yellobyte/LED-Strip-Light-Organ/Doc/BoardBottom.JPG

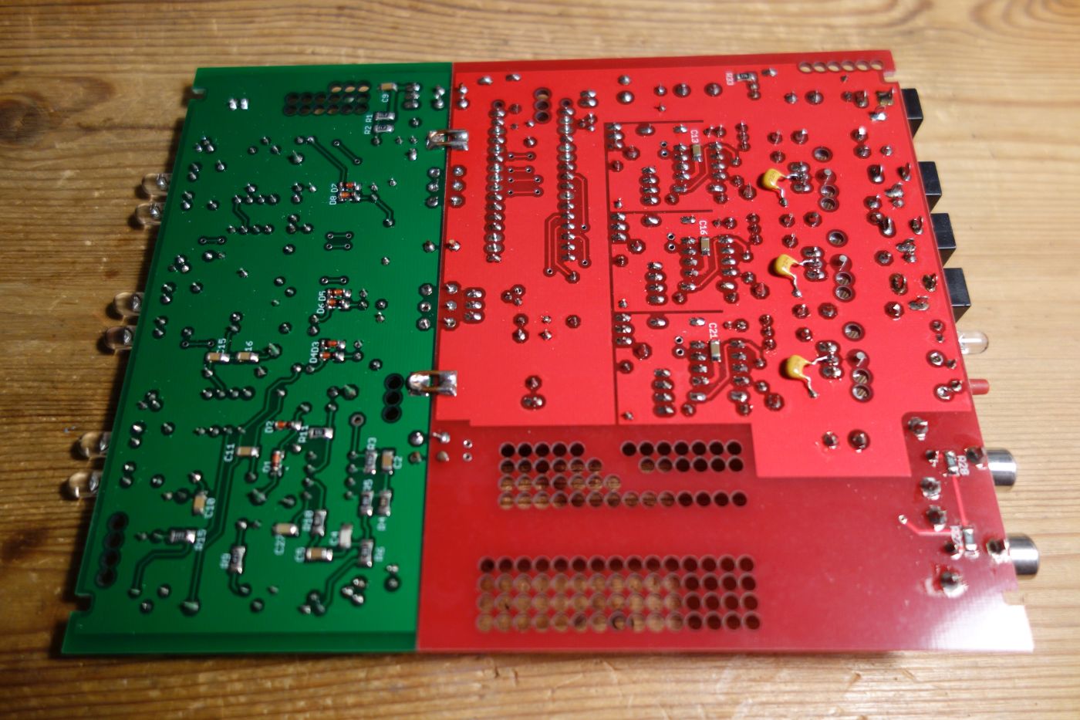
Doc/BoardBottom.JPG
