yellobyte/LED-Strip-Light-Organ/Doc/BoardTop.JPG

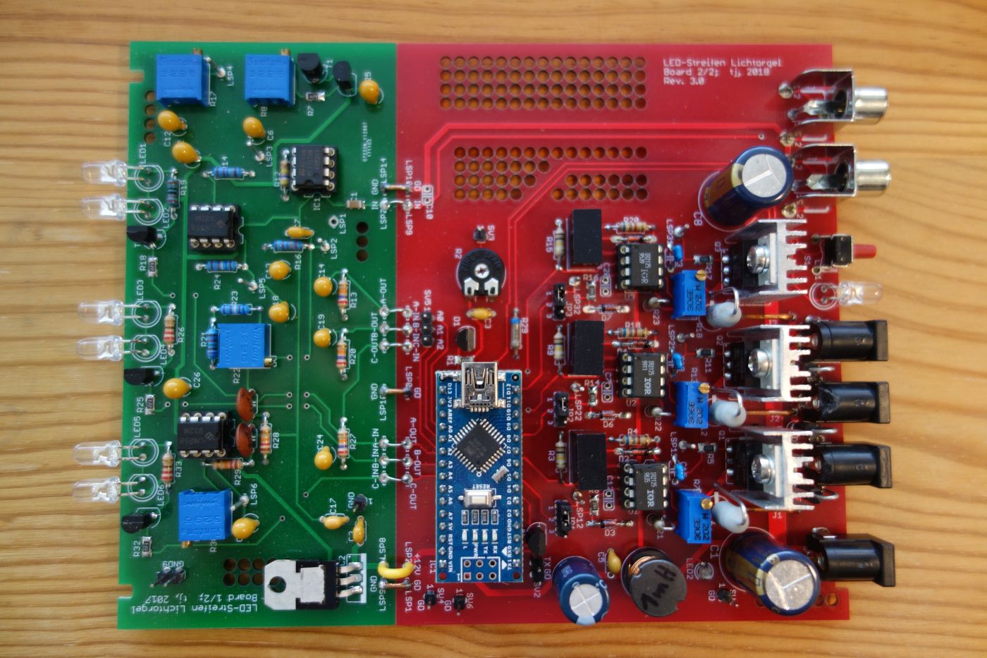
Doc/BoardTop.JPG
