yellobyte/LED-Strip-Light-Organ/Doc/FrontWithControlLEDs.JPG

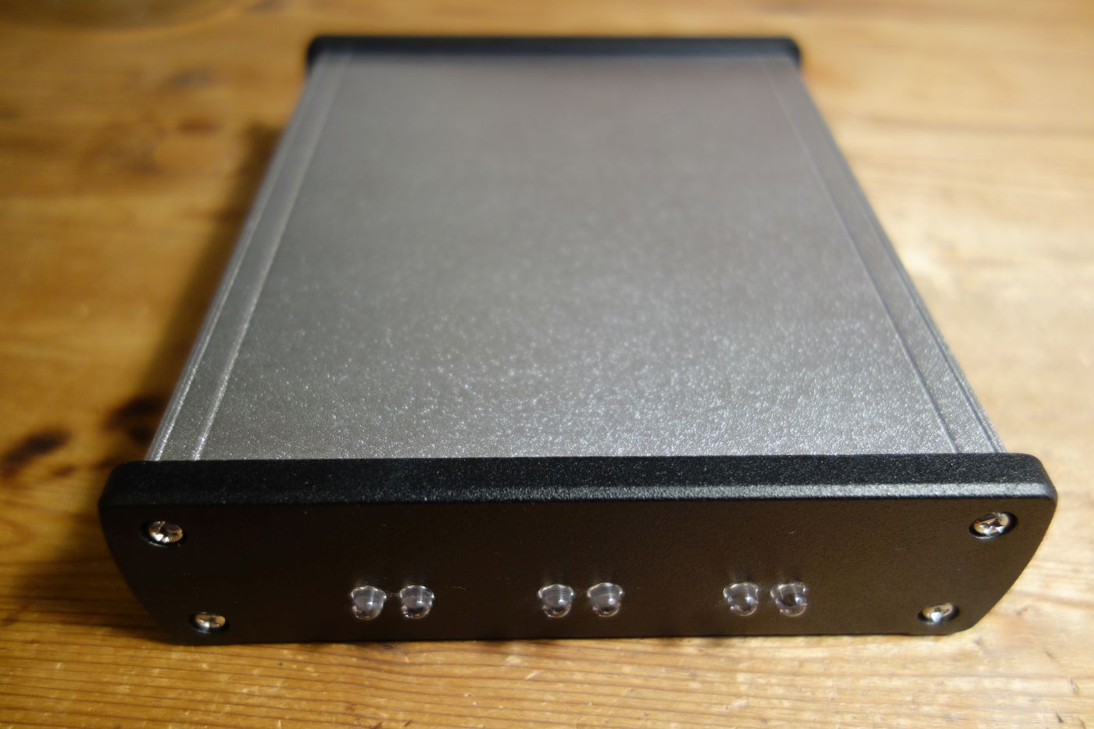
Doc/FrontWithControlLEDs.JPG
