yellobyte/LED-Strip-Light-Organ/EagleFiles/Filter-PCB/Board.JPG

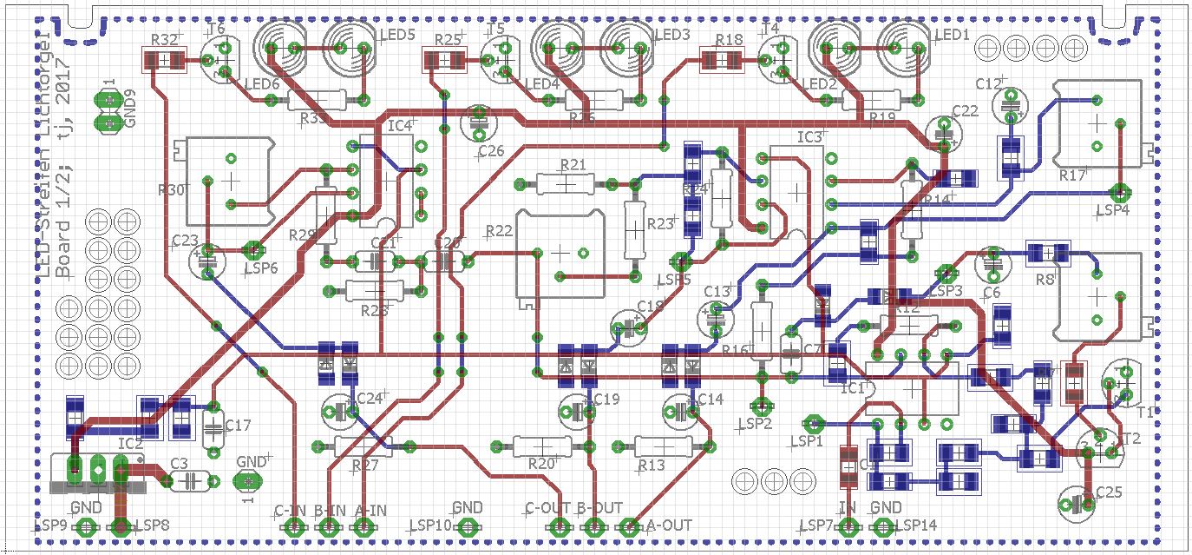
EagleFiles/Filter-PCB/Board.JPG
