yellobyte/LED-Strip-Light-Organ/EagleFiles/Filter-PCB/Filter Calculations/BandPass.JPG

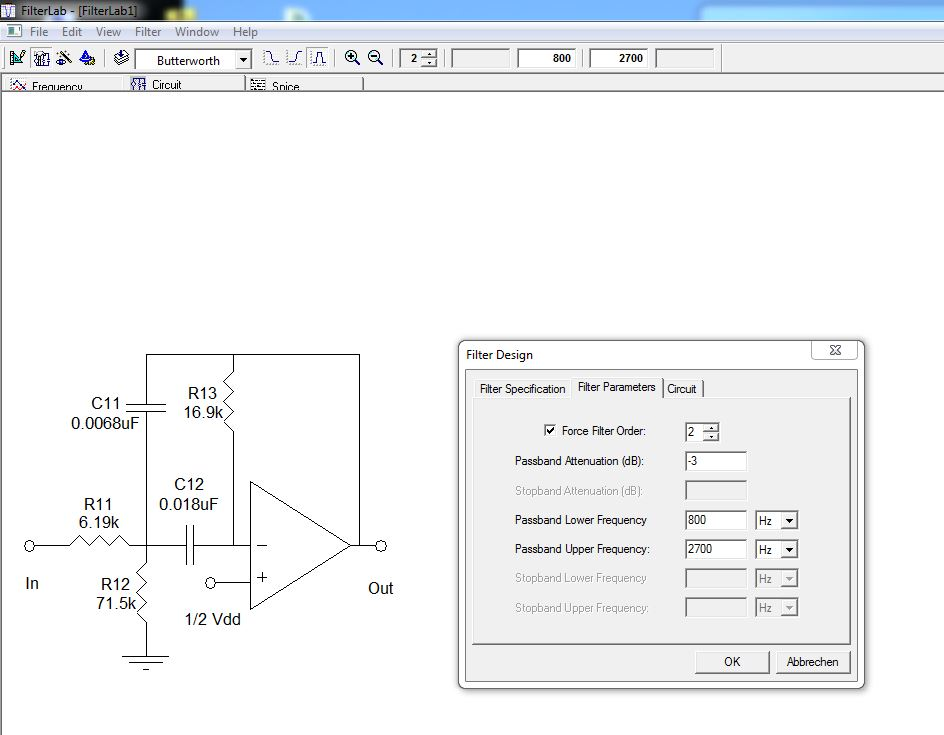
EagleFiles/Filter-PCB/Filter Calculations/BandPass.JPG
