yellobyte/LED-Strip-Light-Organ/EagleFiles/Filter-PCB/Filter Calculations/LowPass.JPG

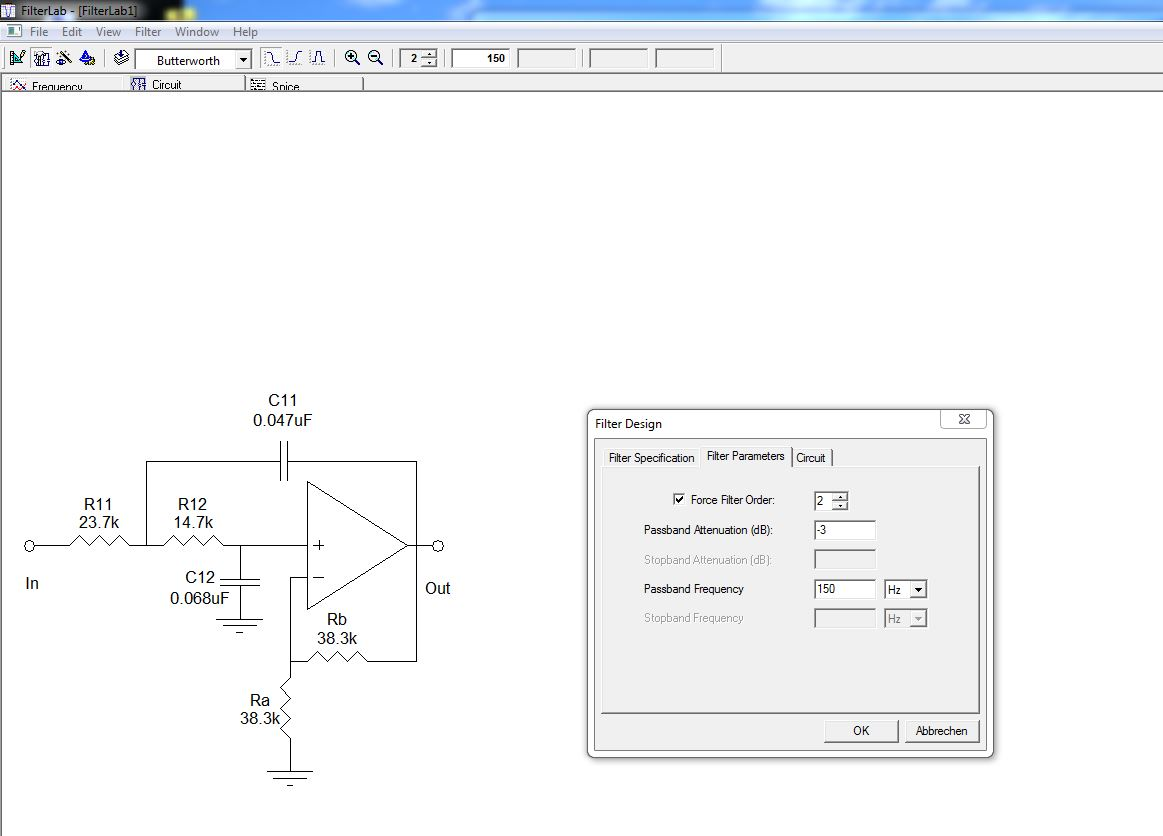
EagleFiles/Filter-PCB/Filter Calculations/LowPass.JPG
