yellobyte/LED-Strip-Light-Organ/EagleFiles/Filter-PCB/NetClasses.JPG

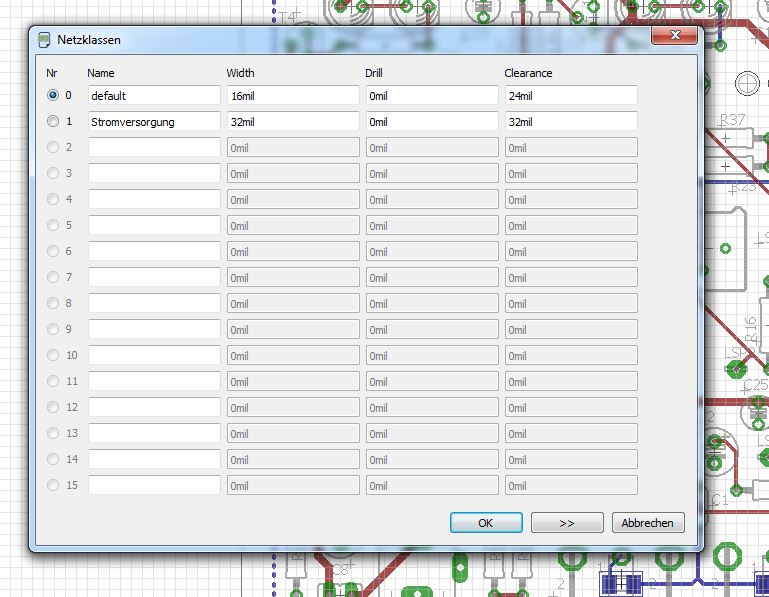
EagleFiles/Filter-PCB/NetClasses.JPG
