yellobyte/LED-Strip-Light-Organ/EagleFiles/Power-PCB/Board.JPG

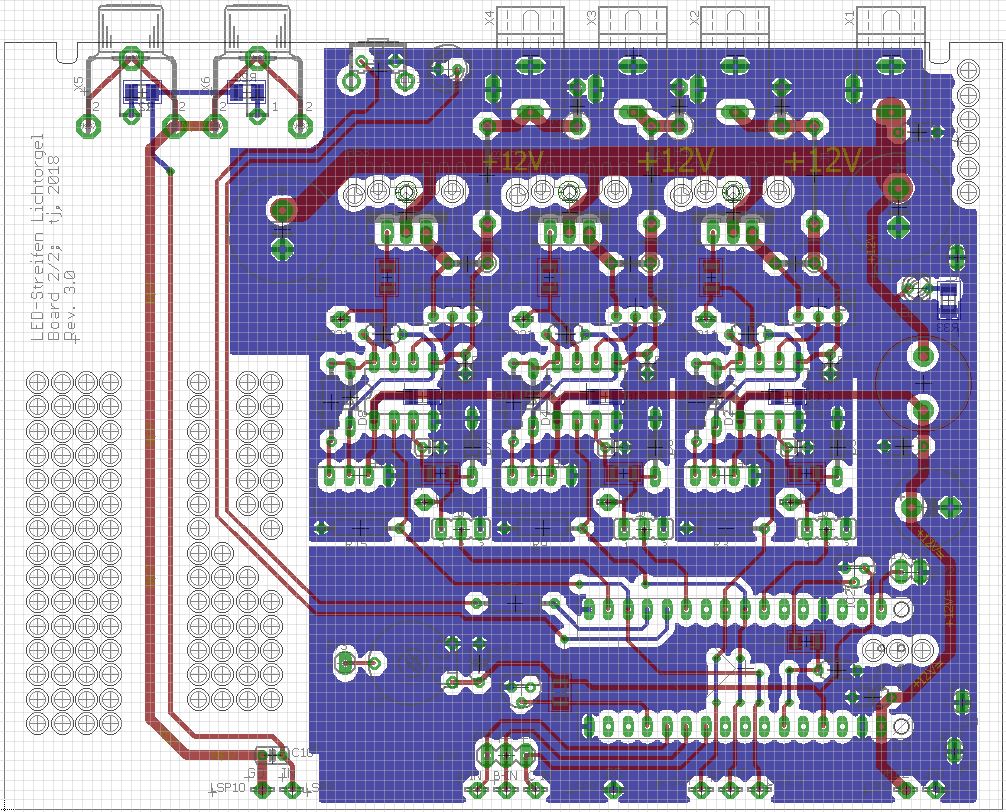
EagleFiles/Power-PCB/Board.JPG
