yellobyte/LED-Strip-Light-Organ/EagleFiles/Power-PCB/NetClasses.JPG

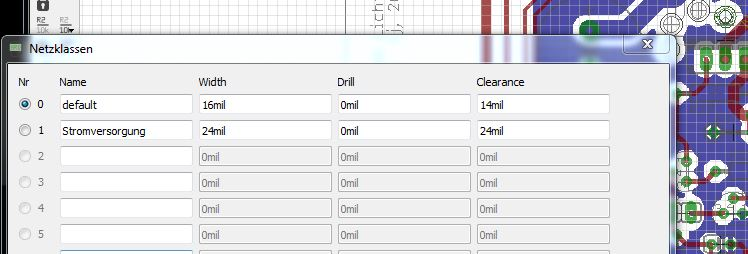
EagleFiles/Power-PCB/NetClasses.JPG
