yellobyte/LED-Strip-Light-Organ/Doc/SPICE Simulation of AGC Stage - step change.JPG

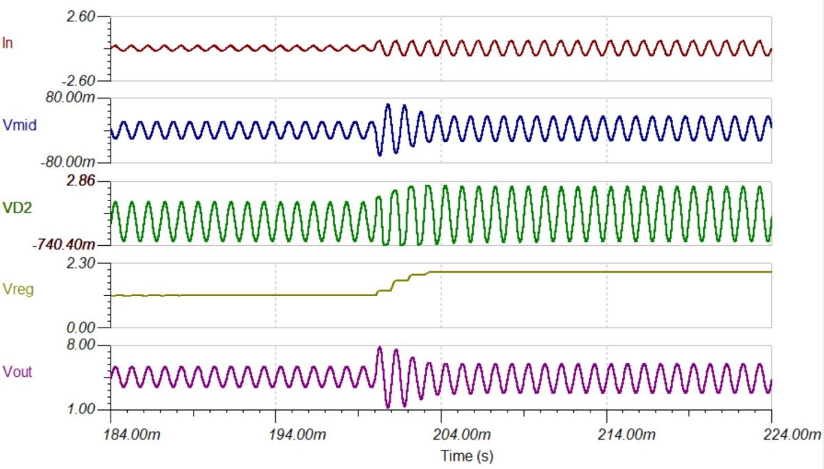
Doc/SPICE Simulation of AGC Stage - step change.JPG
