yellobyte/LED-Strip-Light-Organ/Doc/TestSet.JPG

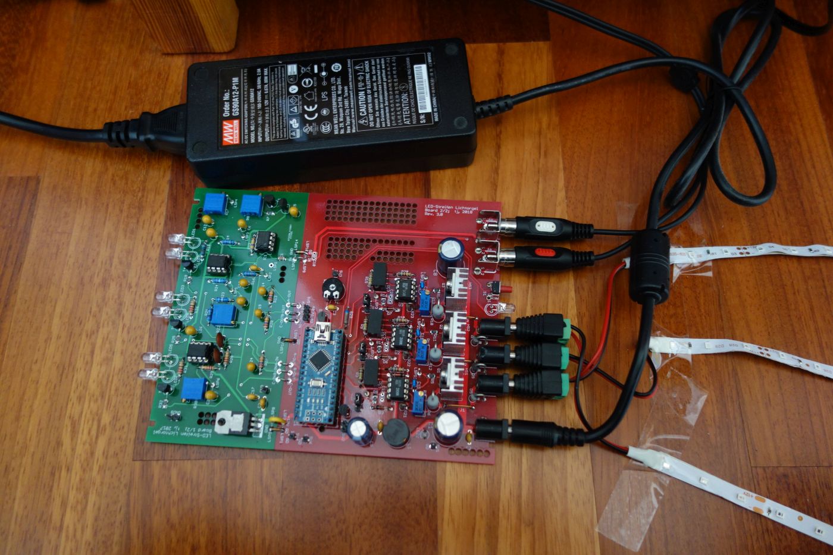
Doc/TestSet.JPG
